nearform/nceubadge/docs-source/content/2017badge/challenges/detect-person-with-pir-sensor.md

---
title: "Detect movement with a PIR Sensor"
weight: 13
date: 2017-10-28T10:29:15+01:00
draft: false
---
### Challenge 13

We have a small number of PIR sensors at the Hacking Table. You can easily wire one of them up to your badge so it can detect motion. Now think of ways you could use that at an event.

You can get started with the [code here](https://www.espruino.com/Motion+Sensing+Lights).
